simonjoh/YAPSCO-10V/ProgKey/RS232/RS232ProgKey.sch

## KiCad design ProgKey/RS232/RS232ProgKey.sch (2019-04-06)

Schematic: RS232ProgKey.sch

Parts:
C1, C2, C3, C5, C6: 10uF
C4: 1uF
J2: DB9
P1: COM_PORT
P2, P3: Vin
P4, P5: 5V_ext
R1, R2: 470
R3, R4: 1K
U1, U2: PHTRANS
U3: 7805
U4: MAX232
X1: USB-B-H; con-usb-3-USB-B-H

Notes on the sheet:
NOT RECOMMENDED FOR NEW BUILDUP!
avec mini 50% de transmission de courant!
Note : veaillez à prendre des optos rapide (>1Mbps)
